Dilanka-ai/Automated-Fish-Pond-Management-System/3D print parts/Images/Assem_1.JPG

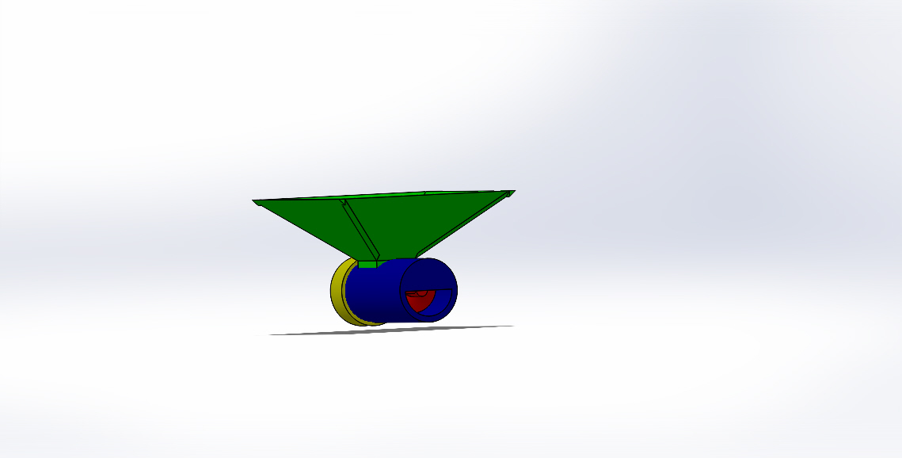
3D print parts/Images/Assem_1.JPG
