Dilanka-ai/Automated-Fish-Pond-Management-System/3D print parts/V1.0/Assem1.SLDASM

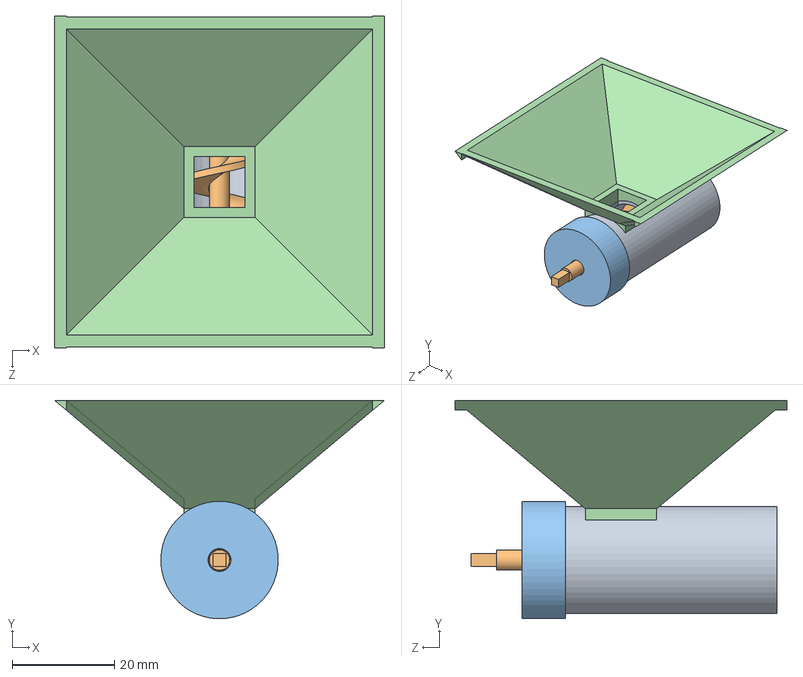
[picture p21: CAD file, 2025-08-20, an earlier design]
3D print parts/V1.0/Assem1.SLDASM
64.6 x 42.8 x 65.0 mm
Spiral Outer cover
Spiral
Cover cup
Container
